theycallmeboxy/lucky/pcb/lucky v1.1/lucky1.1.kicad_sch

## KiCad design pcb/lucky v1.1/lucky1.1.kicad_sch (2024-10-03)

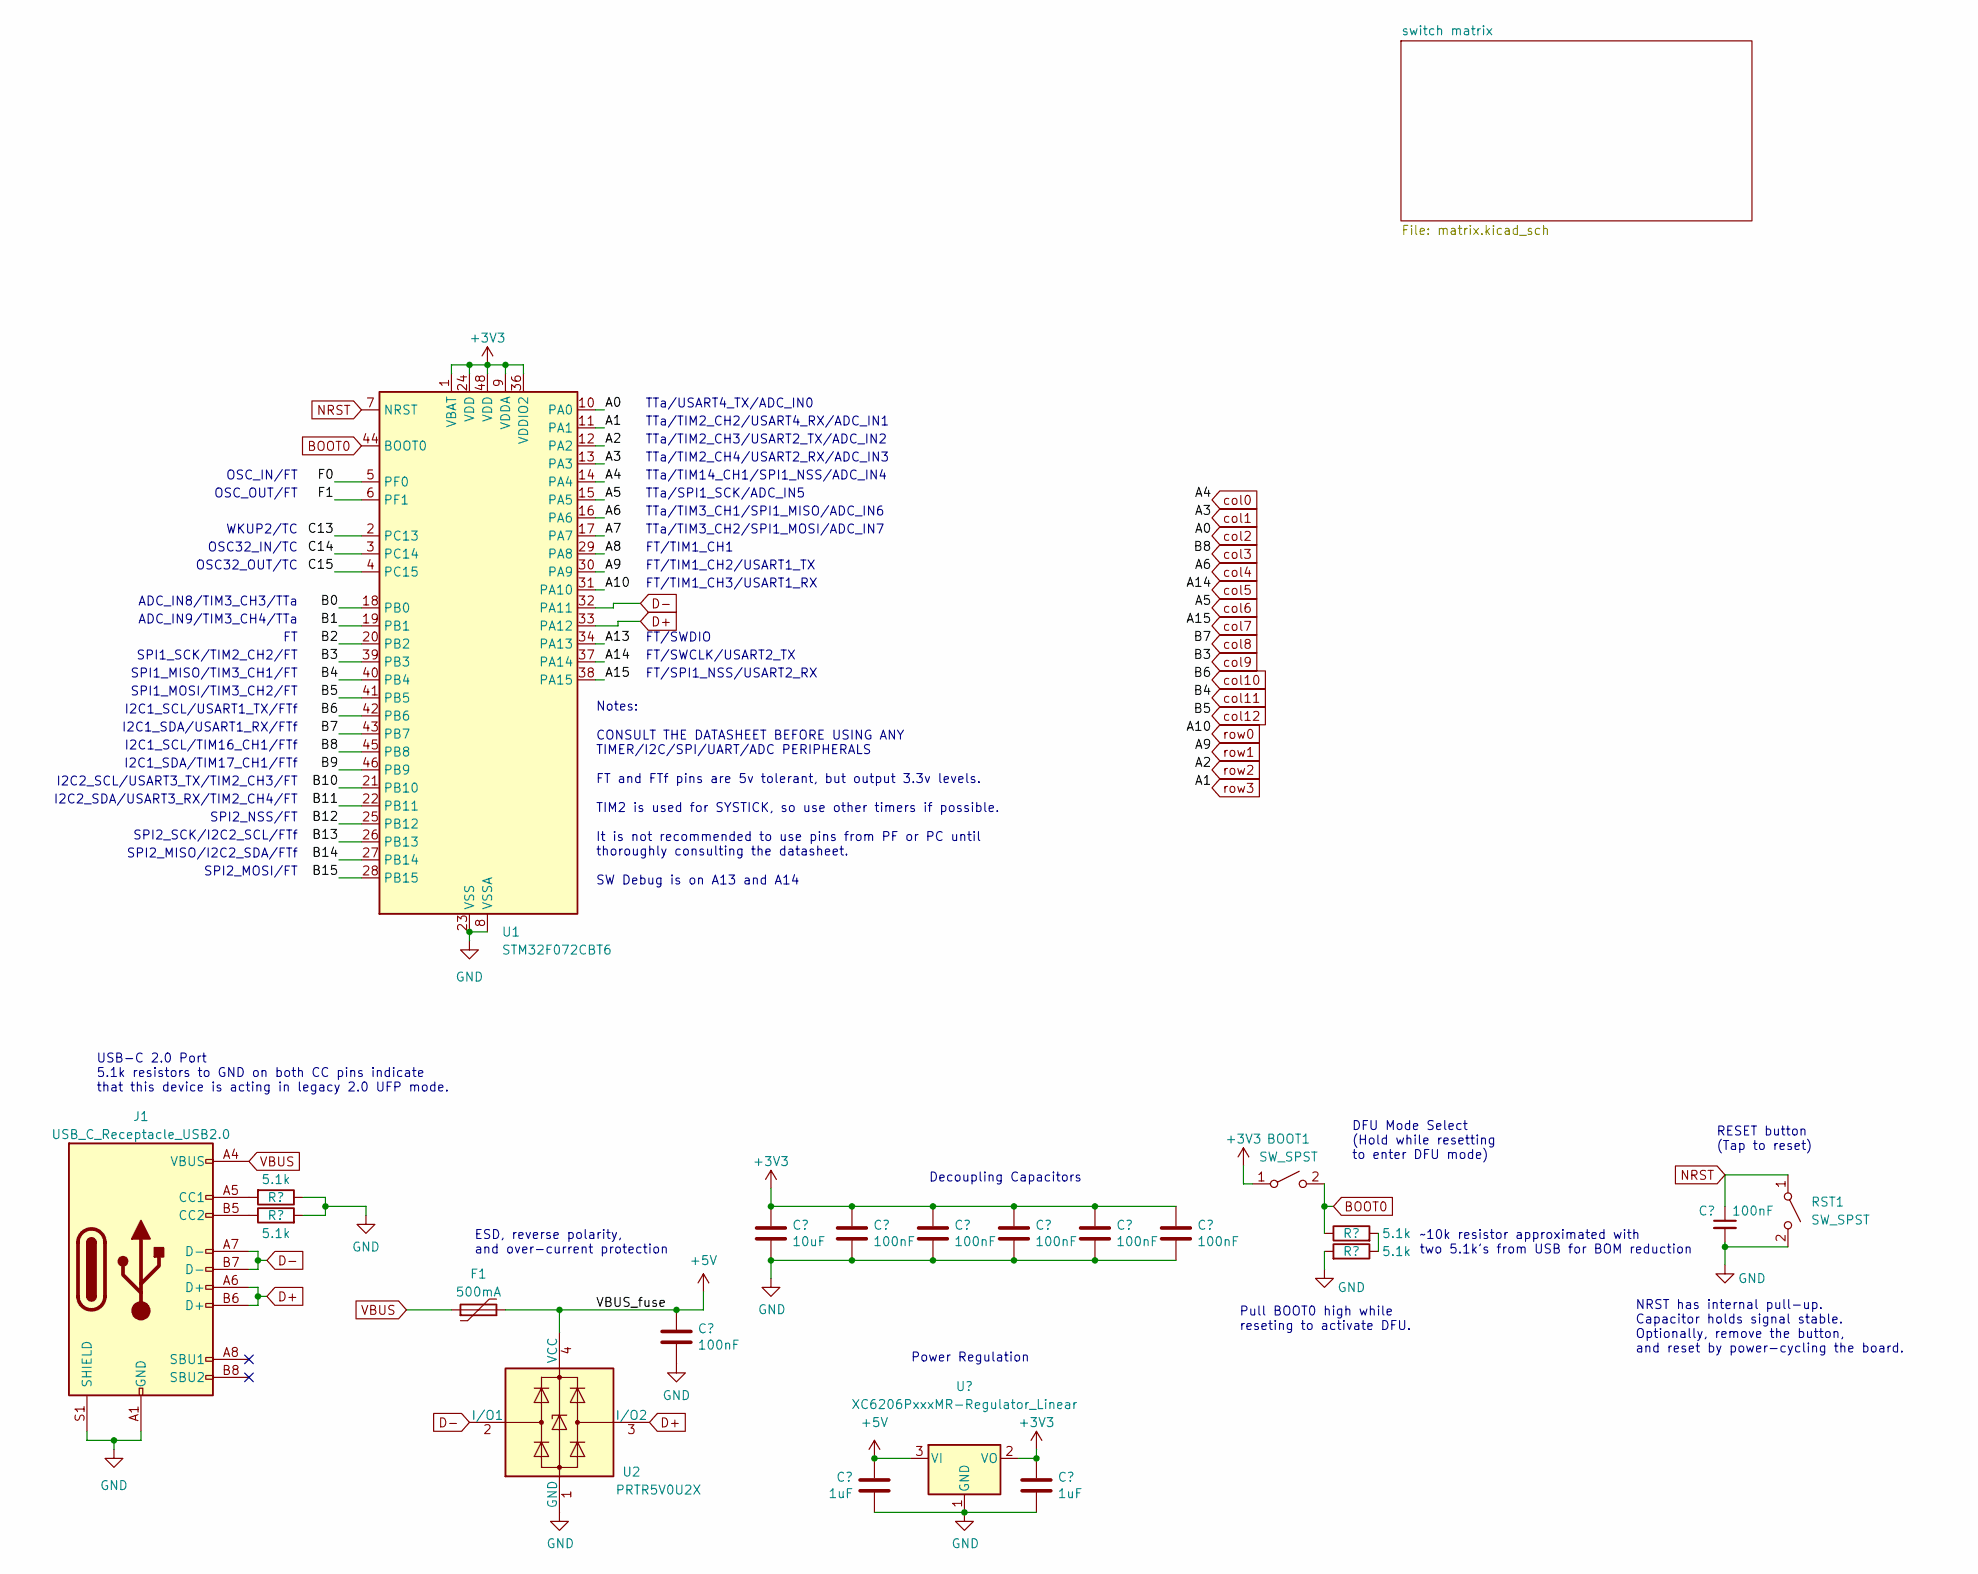
[picture p7: schematic lucky1.1.kicad_sch]

Parts:
BOOT1: SW_SPST; SW_SPST_TL3342
C1, C3, C4, C5, C6, C7, C8: 100nF; C_0402_1005Metric; LCSC C307331
C2: 10uF; C_0603_1608Metric; LCSC C307331
C9, C10: 1uF; C_0402_1005Metric; LCSC C307331
F1: 500mA; Fuse_1206_3216Metric; LCSC C135341
J1: USB_C_Receptacle_USB2.0; USB_C_Receptacle_HRO_TYPE-C-31-M-12; JlcRotOffset 180
R1, R2, R3, R4: 5.1k; R_0402_1005Metric
RST1: SW_SPST; SW_SPST_TL3342
U1: STM32F072CBT6; LQFP-48_7x7mm_P0.5mm; JlcRotOffset 90
U2: PRTR5V0U2X; SOT-143; LCSC C2827688
U3: XC6206PxxxMR-Regulator_Linear; SOT-23; LCSC C5446

Connections:
+3V3: BOOT1.1 (A), C2.1, C3.1, C4.1, C5.1, C6.1, C7.1, C10.1, U1.1 (VBAT), U1.9 (VDDA), U1.24 (VDD), U1.36 (VDDIO2), U1.48 (VDD), U3.2 (VO)
+5V: C8.1, C9.1, F1.2, U2.4 (VCC), U3.3 (VI)
A7: U1.17 (PA7)
A8: U1.29 (PA8)
A13: U1.34 (PA13)
B0: U1.18 (PB0)
B1: U1.19 (PB1)
B2: U1.20 (PB2)
B9: U1.46 (PB9)
B10: U1.21 (PB10)
B11: U1.22 (PB11)
B12: U1.25 (PB12)
B13: U1.26 (PB13)
B14: U1.27 (PB14)
B15: U1.28 (PB15)
BOOT0: BOOT1.2 (B), R3.1, U1.44 (BOOT0)
C13: U1.2 (PC13)
C14: U1.3 (PC14)
C15: U1.4 (PC15)
D+: J1.A6 (D+), J1.B6 (D+), U1.33 (PA12), U2.3 (I/O2)
D-: J1.A7 (D-), J1.B7 (D-), U1.32 (PA11), U2.2 (I/O1)
F0: U1.5 (PF0)
F1: U1.6 (PF1)
GND: C1.2, C2.2, C3.2, C4.2, C5.2, C6.2, C7.2, C8.2, C9.2, C10.2, J1.A1 (GND), J1.A12 (GND), J1.B1 (GND), J1.B12 (GND), J1.S1 (SHIELD), R1.1, R2.2, R4.2, RST1.2 (B), U1.8 (VSSA), U1.23 (VSS), U1.35 (VSS), U1.47 (VSS), U2.1 (GND), U3.1 (GND)
NRST: C1.1, RST1.1 (A), U1.7 (NRST)
unnamed: J1.A5 (CC1), R1.2
unnamed: J1.B5 (CC2), R2.1
unnamed: R3.2, R4.1
VBUS: F1.1, J1.A4 (VBUS), J1.A9 (VBUS), J1.B4 (VBUS), J1.B9 (VBUS)
col0: U1.14 (PA4)
col1: U1.13 (PA3)
col2: U1.10 (PA0)
col3: U1.45 (PB8)
col4: U1.16 (PA6)
col5: U1.37 (PA14)
col6: U1.15 (PA5)
col7: U1.38 (PA15)
col8: U1.43 (PB7)
col9: U1.39 (PB3)
col10: U1.42 (PB6)
col11: U1.40 (PB4)
col12: U1.41 (PB5)
row0: U1.31 (PA10)
row1: U1.30 (PA9)
row2: U1.12 (PA2)
row3: U1.11 (PA1)

Notes on the sheet:
SPI1_SCK/TIM2_CH2/FT
FT/TIM1_CH1
FT/TIM1_CH3/USART1_RX
SPI2_NSS/FT
Notes: CONSULT THE DATASHEET BEFORE USING ANY TIMER/I2C/SPI/UART/ADC PERIPHERALS FT and FTf pins are 5v tolerant, but output 3.3v levels. TIM2 is used for SYSTICK, so use other timers if possible. It is not recommended to use pins from PF or PC until thoroughly consulting the datasheet. SW Debug is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
TTa/TIM2_CH4/USART2_RX/ADC_IN3
NRST has internal pull-up. Capacitor holds signal stable. Optionally, remove the button, and reset by power-cycling the board.
FT/SWDIO
Decoupling Capacitors
SPI1_MOSI/TIM3_CH2/FT
ADC_IN9/TIM3_CH4/TTa
I2C2_SCL/USART3_TX/TIM2_CH3/FT
SPI2_MISO/I2C2_SDA/FTf
FT/SWCLK/USART2_TX
I2C1_SCL/TIM16_CH1/FTf
~10k resistor approximated with two 5.1k's from USB for BOM reduction
TTa/TIM2_CH2/USART4_RX/ADC_IN1
USB-C 2.0 Port 5.1k resistors to GND on both CC pins indicate that this device is acting in legacy 2.0 UFP mode.
TTa/TIM2_CH3/USART2_TX/ADC_IN2
OSC_IN/FT
DFU Mode Select (Hold while resetting to enter DFU mode)
WKUP2/TC
I2C2_SDA/USART3_RX/TIM2_CH4/FT
ADC_IN8/TIM3_CH3/TTa
RESET button (Tap to reset)
Pull BOOT0 high while reseting to activate DFU.
I2C1_SDA/TIM17_CH1/FTf
TTa/SPI1_SCK/ADC_IN5
TTa/TIM3_CH1/SPI1_MISO/ADC_IN6
TTa/TIM3_CH2/SPI1_MOSI/ADC_IN7
OSC32_OUT/TC
FT/SPI1_NSS/USART2_RX
SPI1_MISO/TIM3_CH1/FT
OSC32_IN/TC
TTa/TIM14_CH1/SPI1_NSS/ADC_IN4
I2C1_SDA/USART1_RX/FTf
SPI2_MOSI/FT
FT/TIM1_CH2/USART1_TX
Power Regulation
SPI2_SCK/I2C2_SCL/FTf
OSC_OUT/FT
ESD, reverse polarity, and over-current protection
TTa/USART4_TX/ADC_IN0
I2C1_SCL/USART1_TX/FTf
