theycallmeboxy/lucky/pcb/lucky v1.1/matrix.kicad_sch

## KiCad design pcb/lucky v1.1/matrix.kicad_sch (2024-10-03)

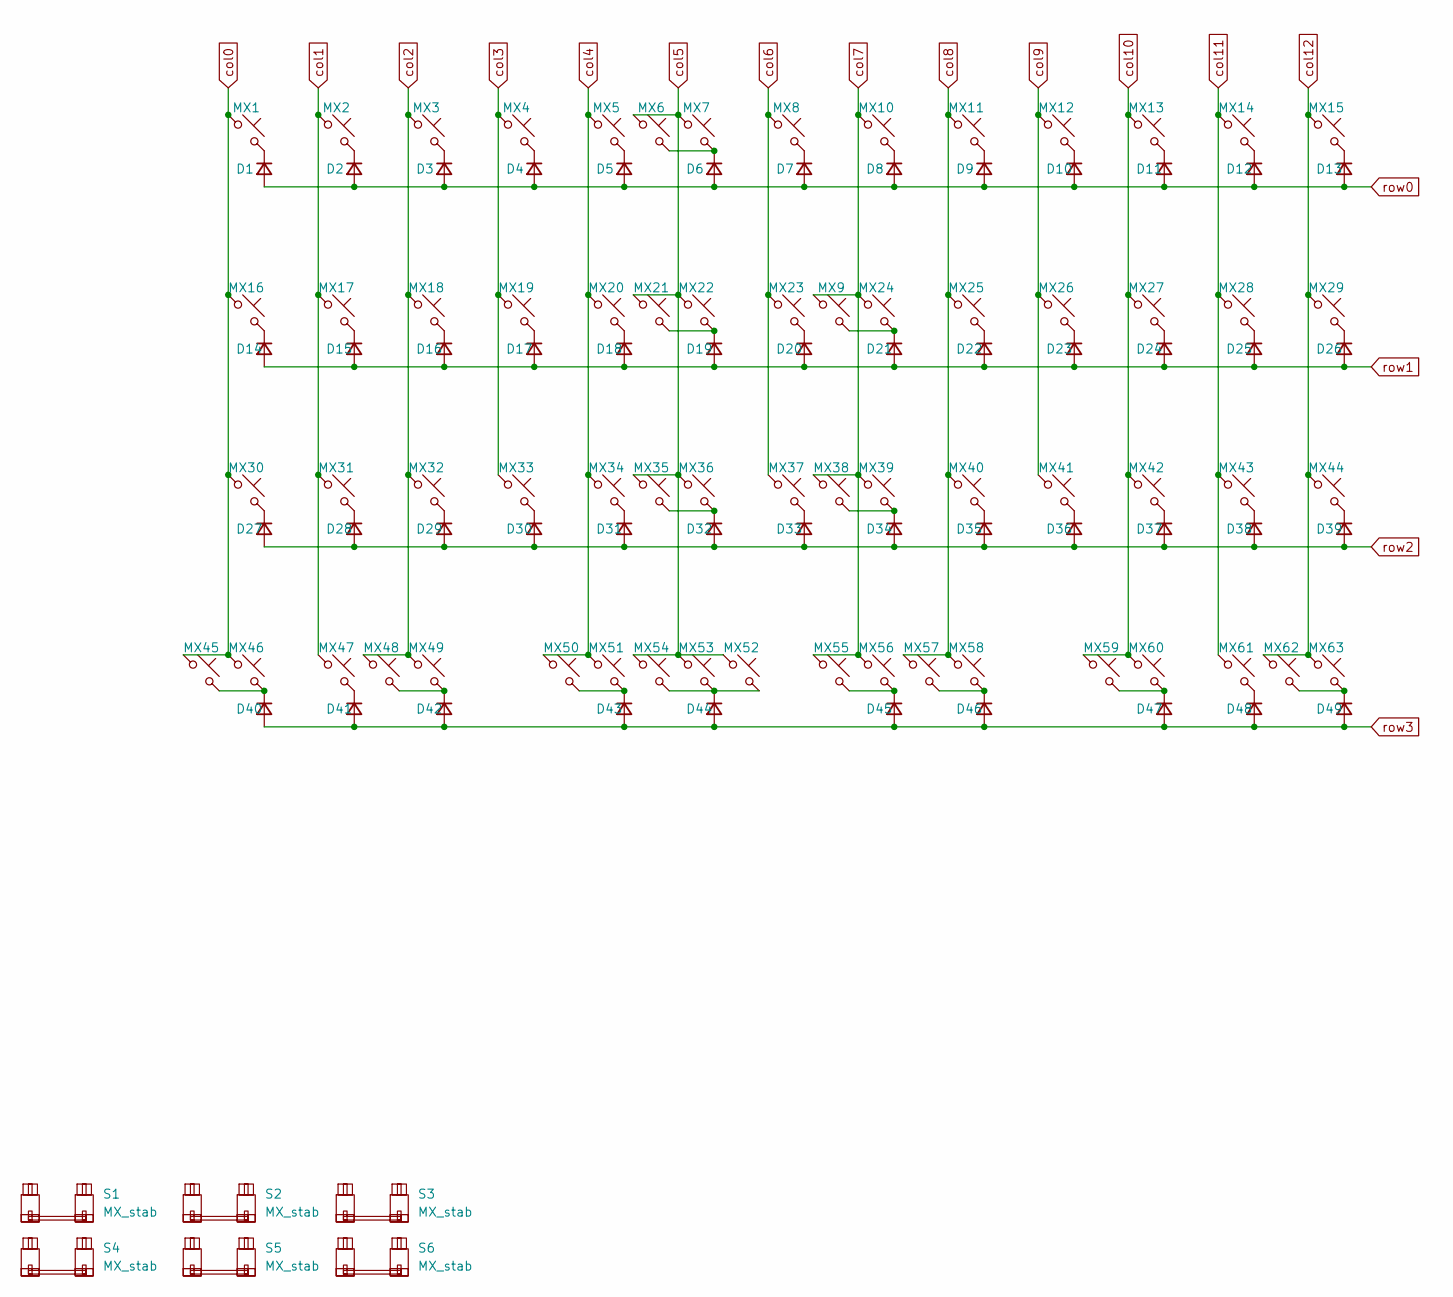
[picture p8: schematic matrix.kicad_sch]

Parts:
D1, D2, D3, D4, D5, D6, D7, D8, D9, D10, D11, D12, D13, D14, D15, D16, D17, D18, D19, D20, D21, D22, D23, D24, D25, D26, D27, D28, D29, D30, D31, D32, D33, D34, D35, D36, D37, D38, D39, D40, D41, D42, D43, D44, D45, D46, D47, D48, D49: D_Small; D_SOD-123
MX1, MX2, MX3, MX4, MX5, MX6, MX7, MX8, MX9, MX10, MX11, MX12, MX13, MX14, MX15, MX16, MX17, MX18, MX19, MX20, MX21, MX22, MX23, MX24, MX25, MX26, MX27, MX28, MX29, MX30, MX31, MX32, MX33, MX34, MX35, MX36, MX37, MX38, MX39, MX40, MX41, MX42, MX43, MX44, MX45, MX46, MX47, MX48, MX49, MX50, MX51, MX52, MX53, MX54, MX55, MX56, MX57, MX58, MX59, MX60, MX61, MX62, MX63: MX_SW_solder; SW_MX_1u
S1, S4: MX_stab; STAB_MX_2.25u
S2, S5: MX_stab; STAB_MX_2.75u
S3: MX_stab; STAB_MX_7u
S6: MX_stab; STAB_MX_ISO

Connections:
unnamed: D1.1 (K), MX1.2
unnamed: D2.1 (K), MX2.2
unnamed: D3.1 (K), MX3.2
unnamed: D4.1 (K), MX4.2
unnamed: D5.1 (K), MX5.2
unnamed: D6.1 (K), MX6.2, MX7.2
unnamed: D7.1 (K), MX8.2
unnamed: D8.1 (K), MX10.2
unnamed: D9.1 (K), MX11.2
unnamed: D10.1 (K), MX12.2
unnamed: D11.1 (K), MX13.2
unnamed: D12.1 (K), MX14.2
unnamed: D13.1 (K), MX15.2
unnamed: D14.1 (K), MX16.2
unnamed: D15.1 (K), MX17.2
unnamed: D16.1 (K), MX18.2
unnamed: D17.1 (K), MX19.2
unnamed: D18.1 (K), MX20.2
unnamed: D19.1 (K), MX21.2, MX22.2
unnamed: D20.1 (K), MX23.2
unnamed: D21.1 (K), MX9.2, MX24.2
unnamed: D22.1 (K), MX25.2
unnamed: D23.1 (K), MX26.2
unnamed: D24.1 (K), MX27.2
unnamed: D25.1 (K), MX28.2
unnamed: D26.1 (K), MX29.2
unnamed: D27.1 (K), MX30.2
unnamed: D28.1 (K), MX31.2
unnamed: D29.1 (K), MX32.2
unnamed: D30.1 (K), MX33.2
unnamed: D31.1 (K), MX34.2
unnamed: D32.1 (K), MX35.2, MX36.2
unnamed: D33.1 (K), MX37.2
unnamed: D34.1 (K), MX38.2, MX39.2
unnamed: D35.1 (K), MX40.2
unnamed: D36.1 (K), MX41.2
unnamed: D37.1 (K), MX42.2
unnamed: D38.1 (K), MX43.2
unnamed: D39.1 (K), MX44.2
unnamed: D40.1 (K), MX45.2, MX46.2
unnamed: D41.1 (K), MX47.2
unnamed: D42.1 (K), MX48.2, MX49.2
unnamed: D43.1 (K), MX50.2, MX51.2
unnamed: D44.1 (K), MX52.2, MX53.2, MX54.2
unnamed: D45.1 (K), MX55.2, MX56.2
unnamed: D46.1 (K), MX57.2, MX58.2
unnamed: D47.1 (K), MX59.2, MX60.2
unnamed: D48.1 (K), MX61.2
unnamed: D49.1 (K), MX62.2, MX63.2
col0: MX1.1, MX16.1, MX30.1, MX45.1, MX46.1
col1: MX2.1, MX17.1, MX31.1, MX47.1
col2: MX3.1, MX18.1, MX32.1, MX48.1, MX49.1
col3: MX4.1, MX19.1, MX33.1
col4: MX5.1, MX20.1, MX34.1, MX50.1, MX51.1
col5: MX6.1, MX7.1, MX21.1, MX22.1, MX35.1, MX36.1, MX52.1, MX53.1, MX54.1
col6: MX8.1, MX23.1, MX37.1
col7: MX9.1, MX10.1, MX24.1, MX38.1, MX39.1, MX55.1, MX56.1
col8: MX11.1, MX25.1, MX40.1, MX57.1, MX58.1
col9: MX12.1, MX26.1, MX41.1
col10: MX13.1, MX27.1, MX42.1, MX59.1, MX60.1
col11: MX14.1, MX28.1, MX43.1, MX61.1
col12: MX15.1, MX29.1, MX44.1, MX62.1, MX63.1
row0: D1.2 (A), D2.2 (A), D3.2 (A), D4.2 (A), D5.2 (A), D6.2 (A), D7.2 (A), D8.2 (A), D9.2 (A), D10.2 (A), D11.2 (A), D12.2 (A), D13.2 (A)
row1: D14.2 (A), D15.2 (A), D16.2 (A), D17.2 (A), D18.2 (A), D19.2 (A), D20.2 (A), D21.2 (A), D22.2 (A), D23.2 (A), D24.2 (A), D25.2 (A), D26.2 (A)
row2: D27.2 (A), D28.2 (A), D29.2 (A), D30.2 (A), D31.2 (A), D32.2 (A), D33.2 (A), D34.2 (A), D35.2 (A), D36.2 (A), D37.2 (A), D38.2 (A), D39.2 (A)
row3: D40.2 (A), D41.2 (A), D42.2 (A), D43.2 (A), D44.2 (A), D45.2 (A), D46.2 (A), D47.2 (A), D48.2 (A), D49.2 (A)
